Arnaud-Le-Cossec/EPOT/Cahier_Des_Charges/EPOT_SCHEMA_BLOC_SIMPLIFIE.png

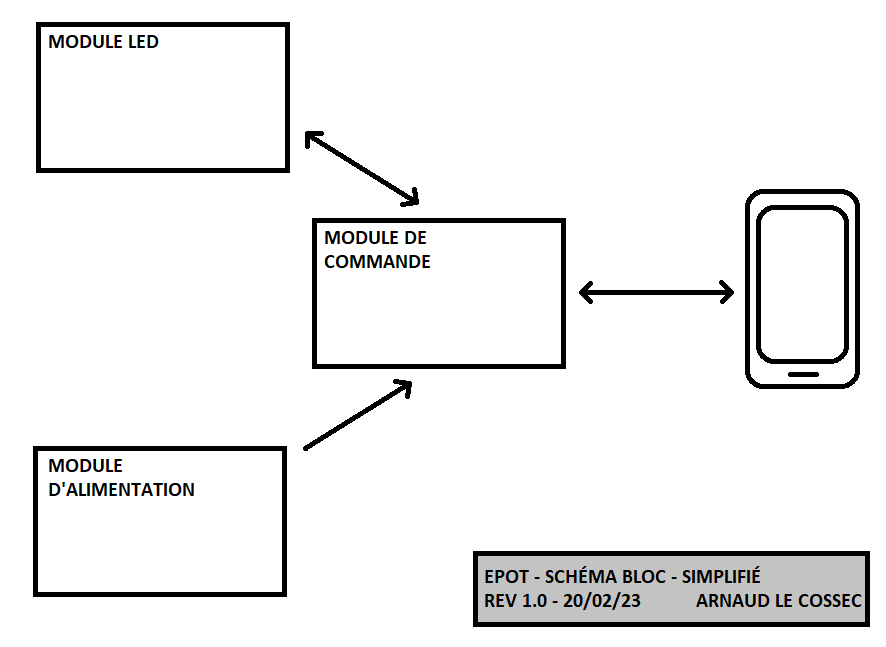
Cahier_Des_Charges/EPOT_SCHEMA_BLOC_SIMPLIFIE.png
