Arnaud-Le-Cossec/EPOT/Codes_sources/EPOT_ESP_Firmware_source_code/EPOT_Firmware_structure_simplifie.png

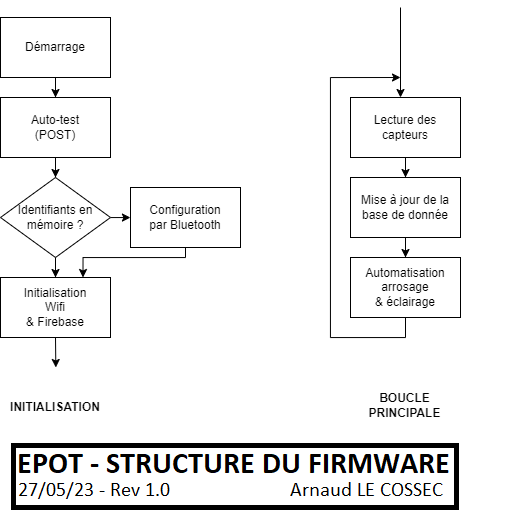
Codes_sources/EPOT_ESP_Firmware_source_code/EPOT_Firmware_structure_simplifie.png
