Arnaud-Le-Cossec/EPOT/Mechanique/EPOT_Tube_PVC_Dimentions.png

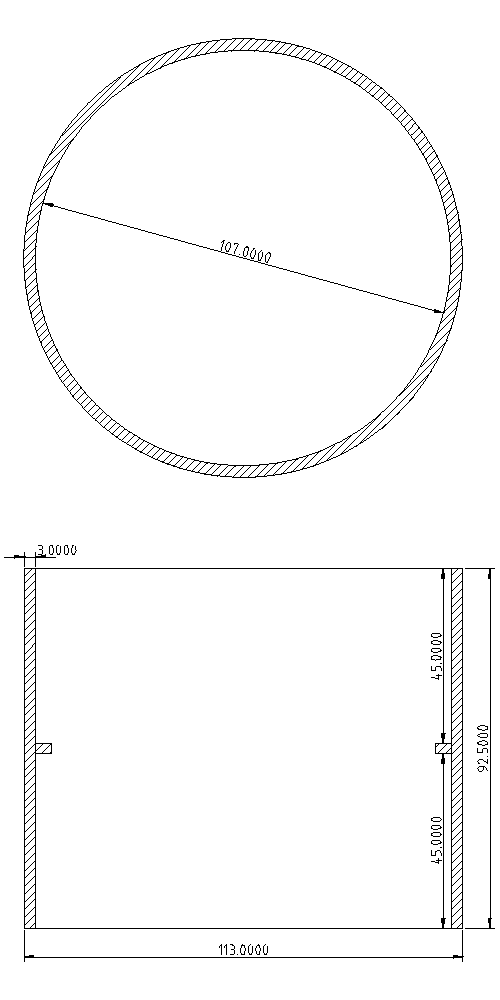
Mechanique/EPOT_Tube_PVC_Dimentions.png
