Arnaud-Le-Cossec/EPOT/Photo/EPOT_img2.jpg

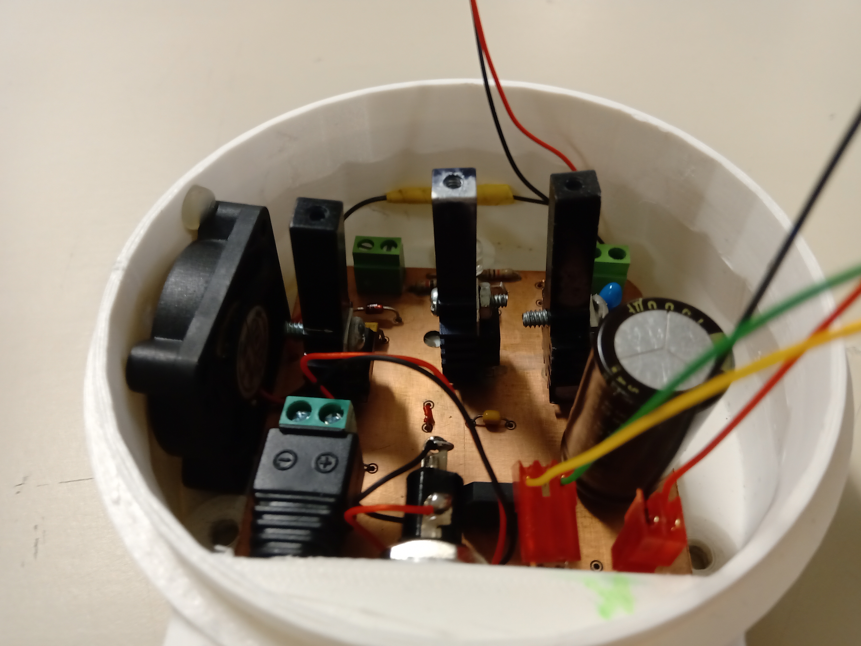
Photo/EPOT_img2.jpg
