Arnaud-Le-Cossec/EPOT/Planninfication/EPOT_Plannifiaction_13_03.png

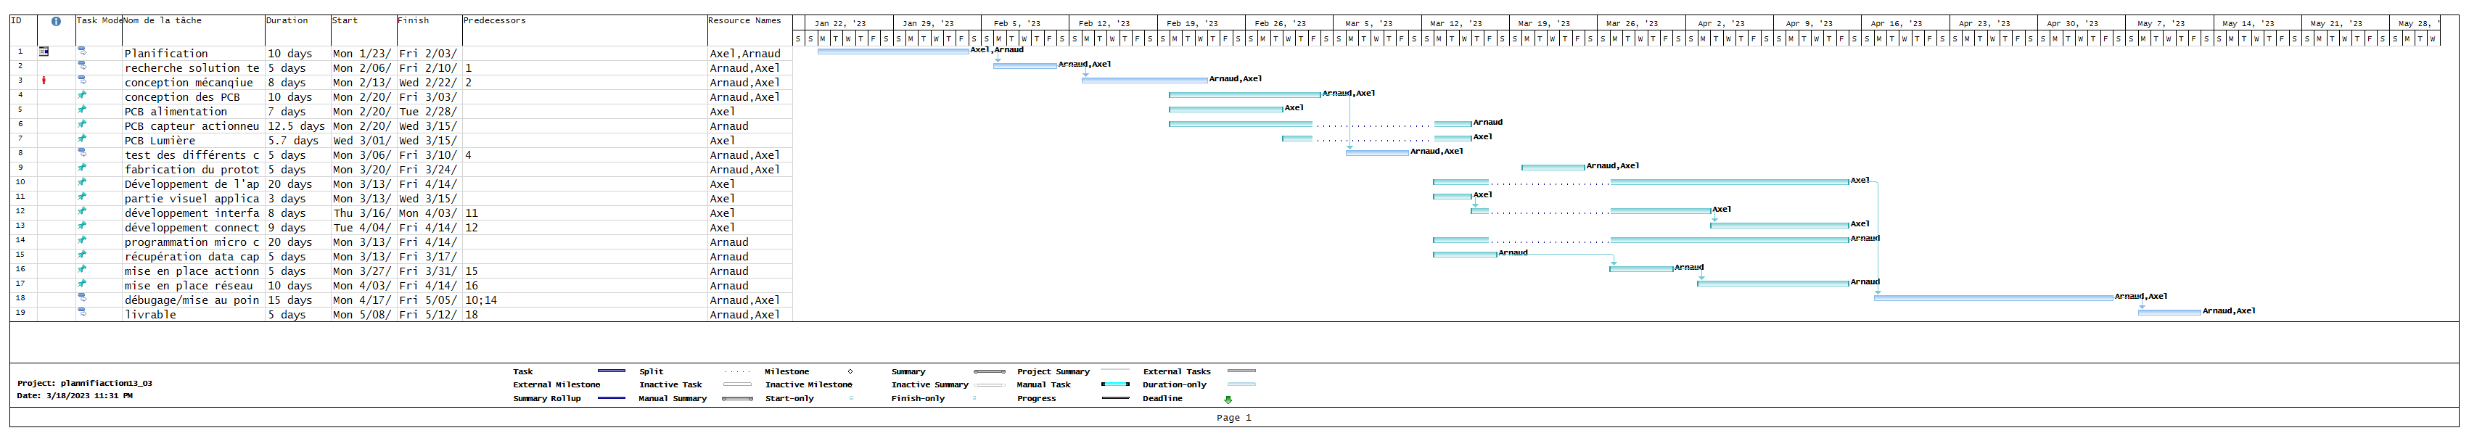
Planninfication/EPOT_Plannifiaction_13_03.png
