Arnaud-Le-Cossec/EPOT/Schema_PCB/EPOT_COMMAND_BOARD/EPOT_CMD_MODULE.png

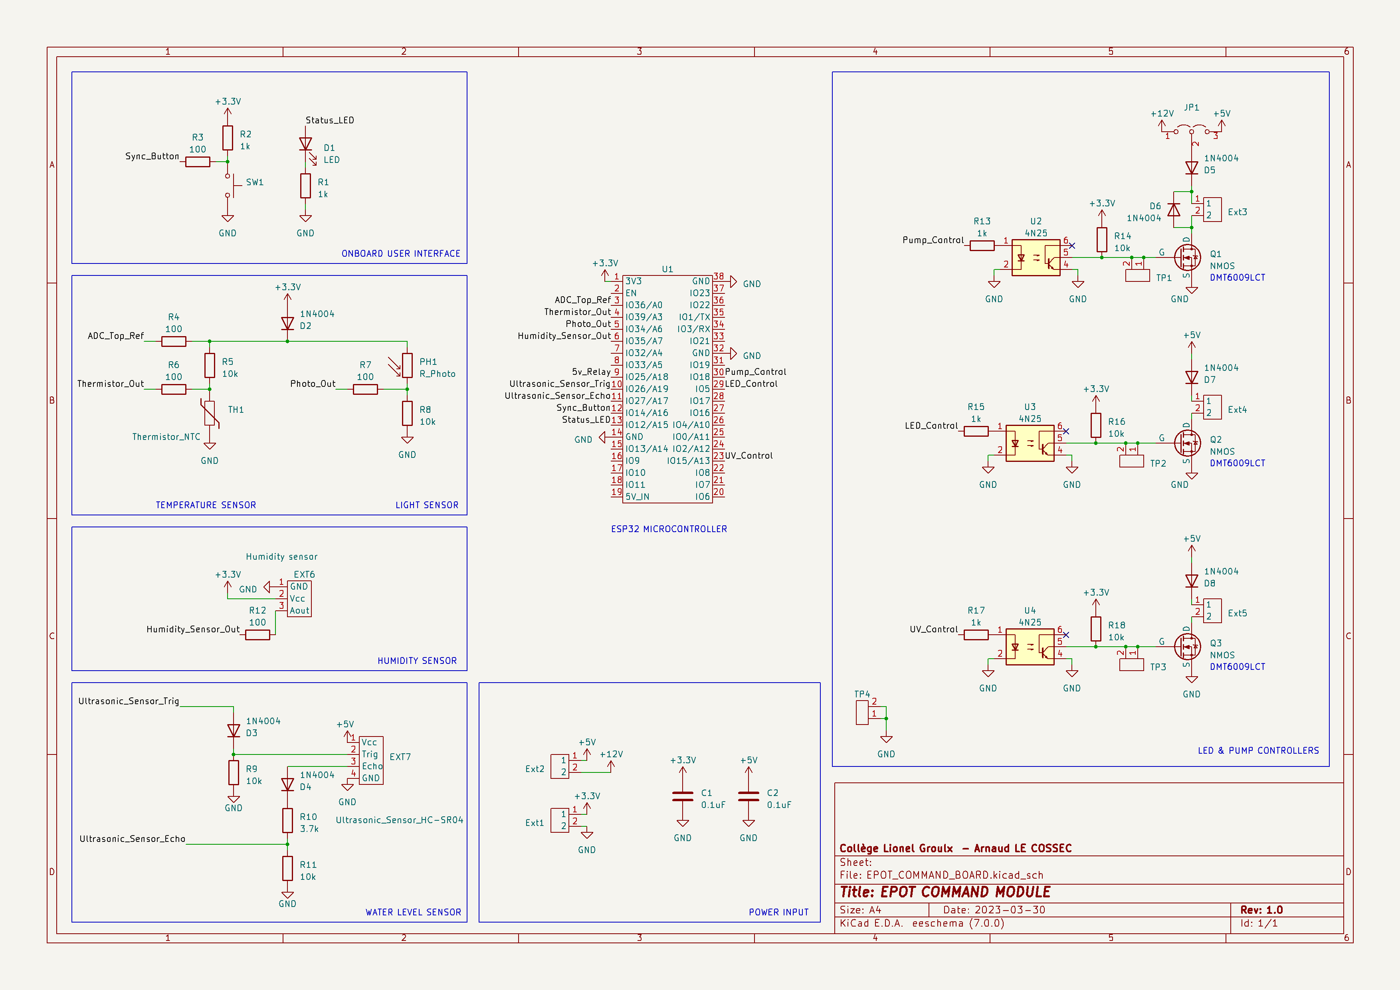
Schema_PCB/EPOT_COMMAND_BOARD/EPOT_CMD_MODULE.png
