Arnaud-Le-Cossec/EPOT/Schema_PCB/EPOT_Interconnections.png

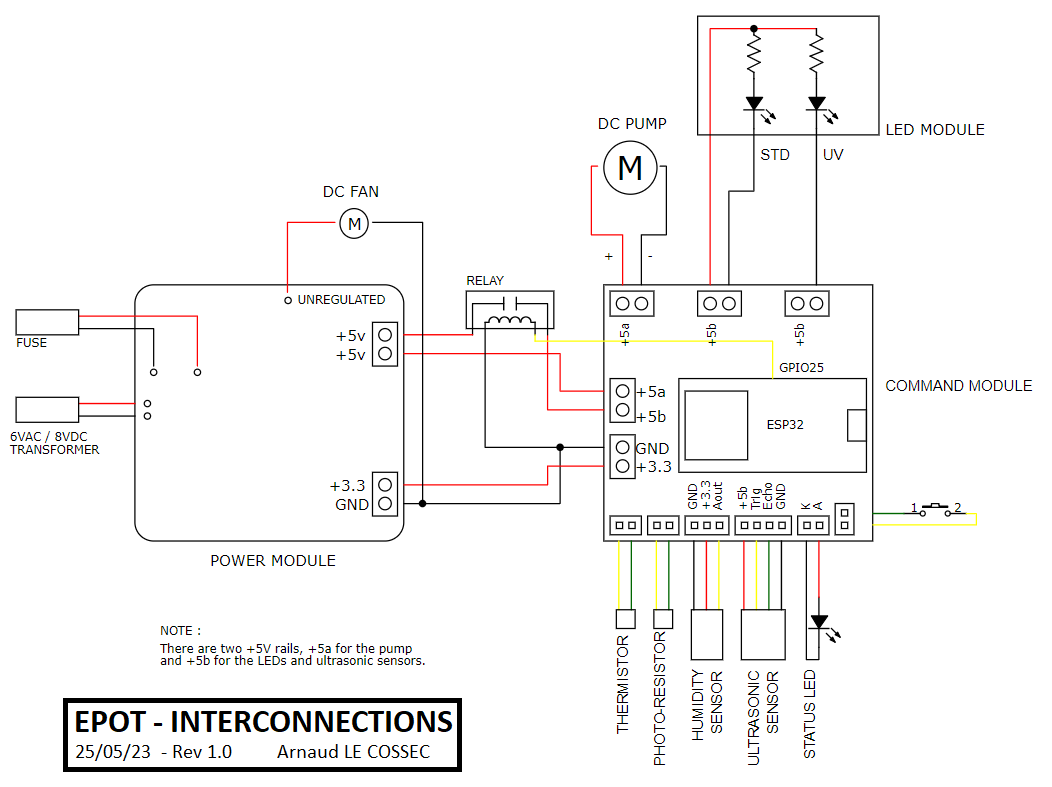
Schema_PCB/EPOT_Interconnections.png
